photobooth-app/photobooth-buzzer/cad/solidworks/inlet-onoff.SLDPRT

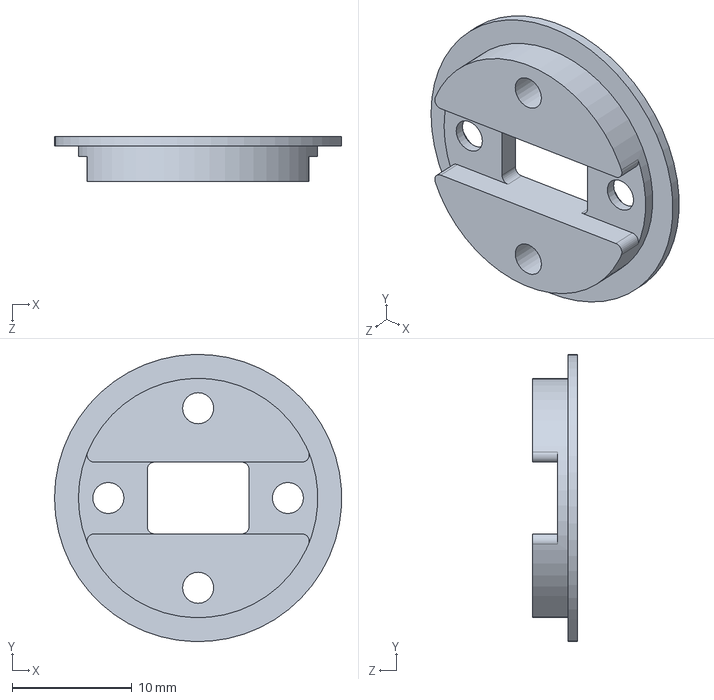
[picture p6: CAD file, 2024-09-16]
cad/solidworks/inlet-onoff.SLDPRT
24.0 x 24.0 x 3.80 mm
