photobooth-app/photobooth-buzzer/cad/solidworks/inlet.SLDPRT

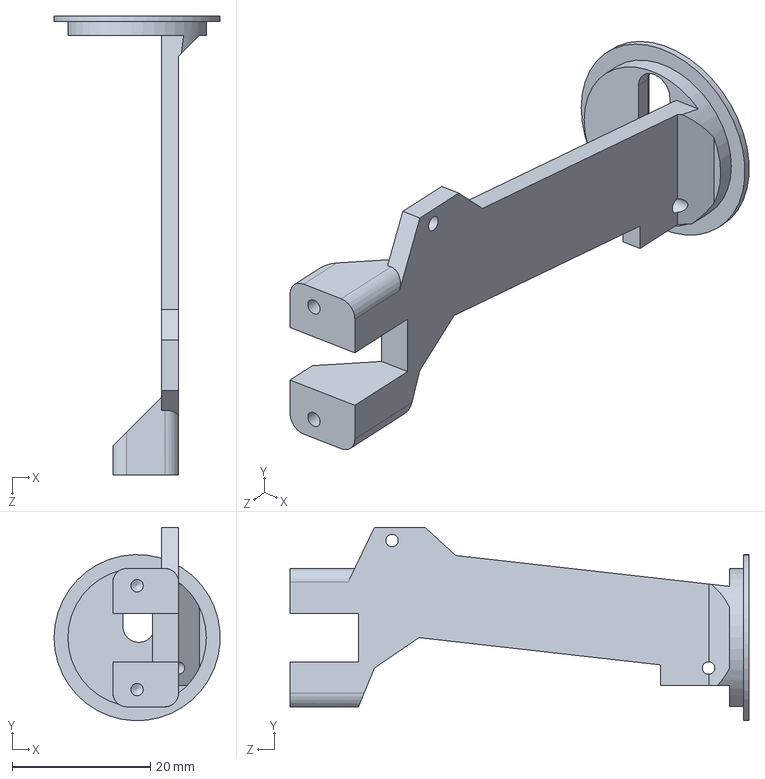
[picture p7: CAD file, 2024-09-16]
cad/solidworks/inlet.SLDPRT
24.0 x 27.9 x 66.3 mm
