photobooth-app/photobooth-buzzer/cad/solidworks/adafruit-feather-esp32-s3.SLDPRT

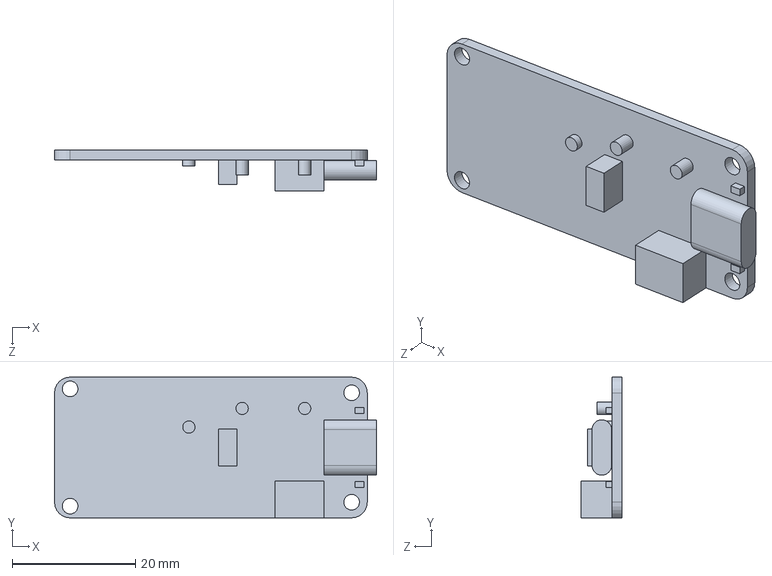
[picture p8: CAD file, 2024-09-16]
cad/solidworks/adafruit-feather-esp32-s3.SLDPRT
52.3 x 22.9 x 6.60 mm
