photobooth-app/photobooth-buzzer/cad/solidworks/switch.SLDPRT

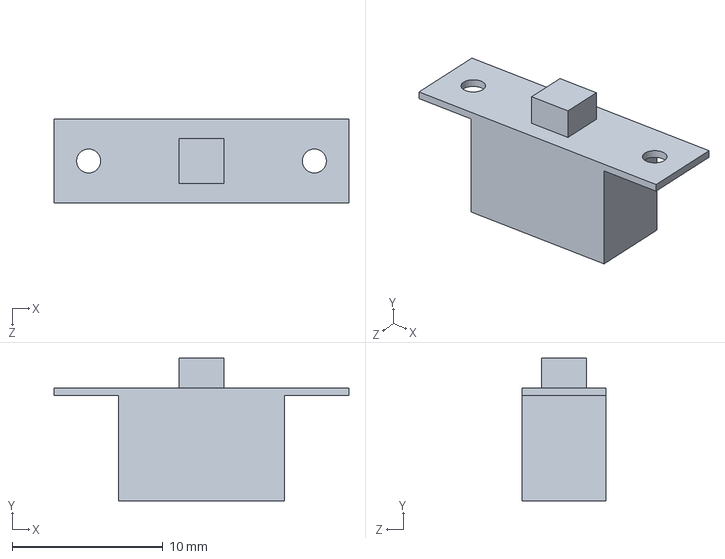
[picture p9: CAD file, 2023-08-15]
cad/solidworks/switch.SLDPRT
19.6 x 9.50 x 5.60 mm
