photobooth-app/photobooth-buzzer/cad/solidworks/buzzer-base.SLDPRT

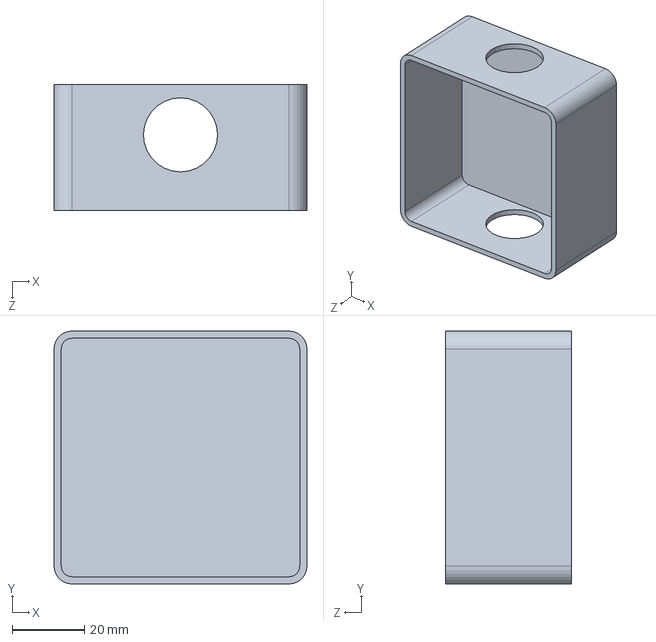
[picture p10: CAD file, 2023-08-15]
cad/solidworks/buzzer-base.SLDPRT
70.0 x 70.0 x 35.0 mm
