photobooth-app/photobooth-buzzer/cad/solidworks/buzzer-top.SLDPRT

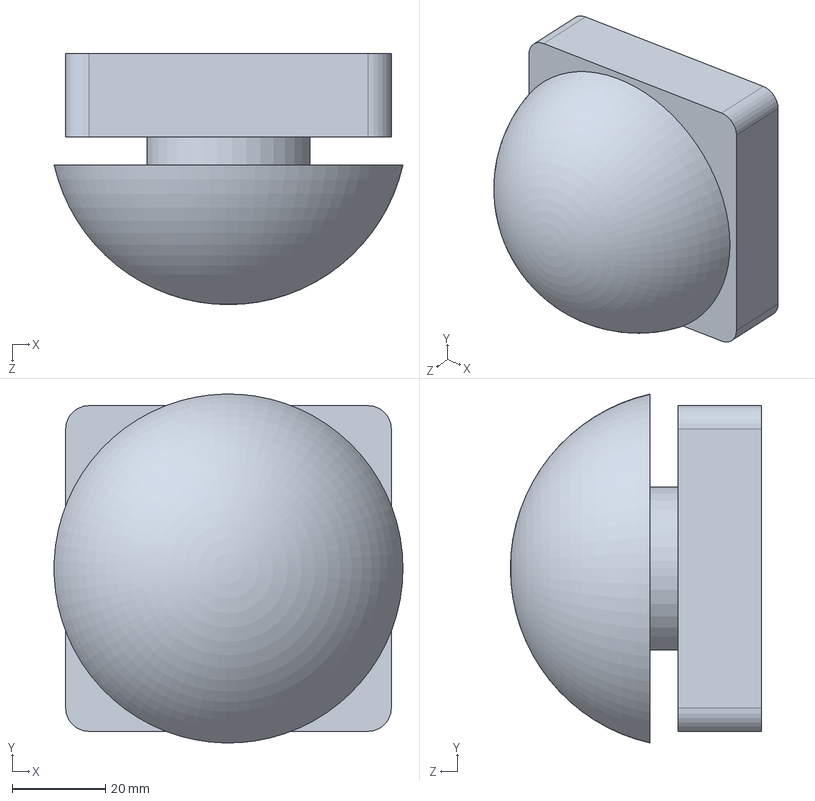
[picture p11: CAD file, 2023-08-11]
cad/solidworks/buzzer-top.SLDPRT
75.0 x 75.0 x 54.0 mm
