photobooth-app/photobooth-buzzer/cad/solidworks/lolin32-lite-1.snapshot.18/Lolin 32 Lite Board.SLDASM

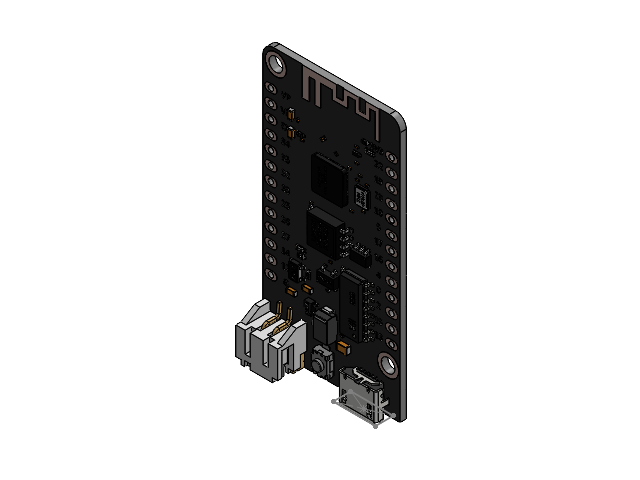
[picture p12: CAD file, 2023-08-11]
cad/solidworks/lolin32-lite-1.snapshot.18/Lolin 32 Lite Board.SLDASM
JST-S2B-PH-SM4-TB
MicroUSB v1
3x4x2 tact button v1
Refdes
Cathode
Anode
ESP32_DOWDQ6_rev1
0603 LED v7 x 2
CH340C
40.00 MHz Oscillator
TP4054-SOT23
T25S32-SOP
ME6211-SOT23
A1SHB-SOT23
SOT23-6_PIN-GENERIC
Resistor 0402 x 6
Lolin 32 Lite Board
Lolin 32 Lite Board-27
Lolin 32 Lite Board-28
Lolin 32 Lite Board-29
Lolin 32 Lite Board-30
Lolin 32 Lite Board-31
Lolin 32 Lite Board-32
Lolin 32 Lite Board-33
Lolin 32 Lite Board-34
Lolin 32 Lite Board-35
Lolin 32 Lite Board-36
Lolin 32 Lite Board-37
Lolin 32 Lite Board-38
Lolin 32 Lite Board-39
Lolin 32 Lite Board-40
Lolin 32 Lite Board-41
Lolin 32 Lite Board-42
Lolin 32 Lite Board-43
Lolin 32 Lite Board-44
Lolin 32 Lite Board-45
Lolin 32 Lite Board-46
Lolin 32 Lite Board-47
Lolin 32 Lite Board-48
Lolin 32 Lite Board-49
Lolin 32 Lite Board-50
Lolin 32 Lite Board-51
Lolin 32 Lite Board-52
Lolin 32 Lite Board-53
Lolin 32 Lite Board-54
Lolin 32 Lite Board-55
Lolin 32 Lite Board-56
Lolin 32 Lite Board-57
Lolin 32 Lite Board-58
Lolin 32 Lite Board-59
Lolin 32 Lite Board-60
Lolin 32 Lite Board-61
Lolin 32 Lite Board-62
Lolin 32 Lite Board-63
Lolin 32 Lite Board-64
Lolin 32 Lite Board-65
Lolin 32 Lite Board-66
Lolin 32 Lite Board-67
Lolin 32 Lite Board-68
Lolin 32 Lite Board-69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
